mepland/chance_of_showers/media/ana_outputs/mean_pressure_value_normalized_vs_time_of_week_recent_mornings.png

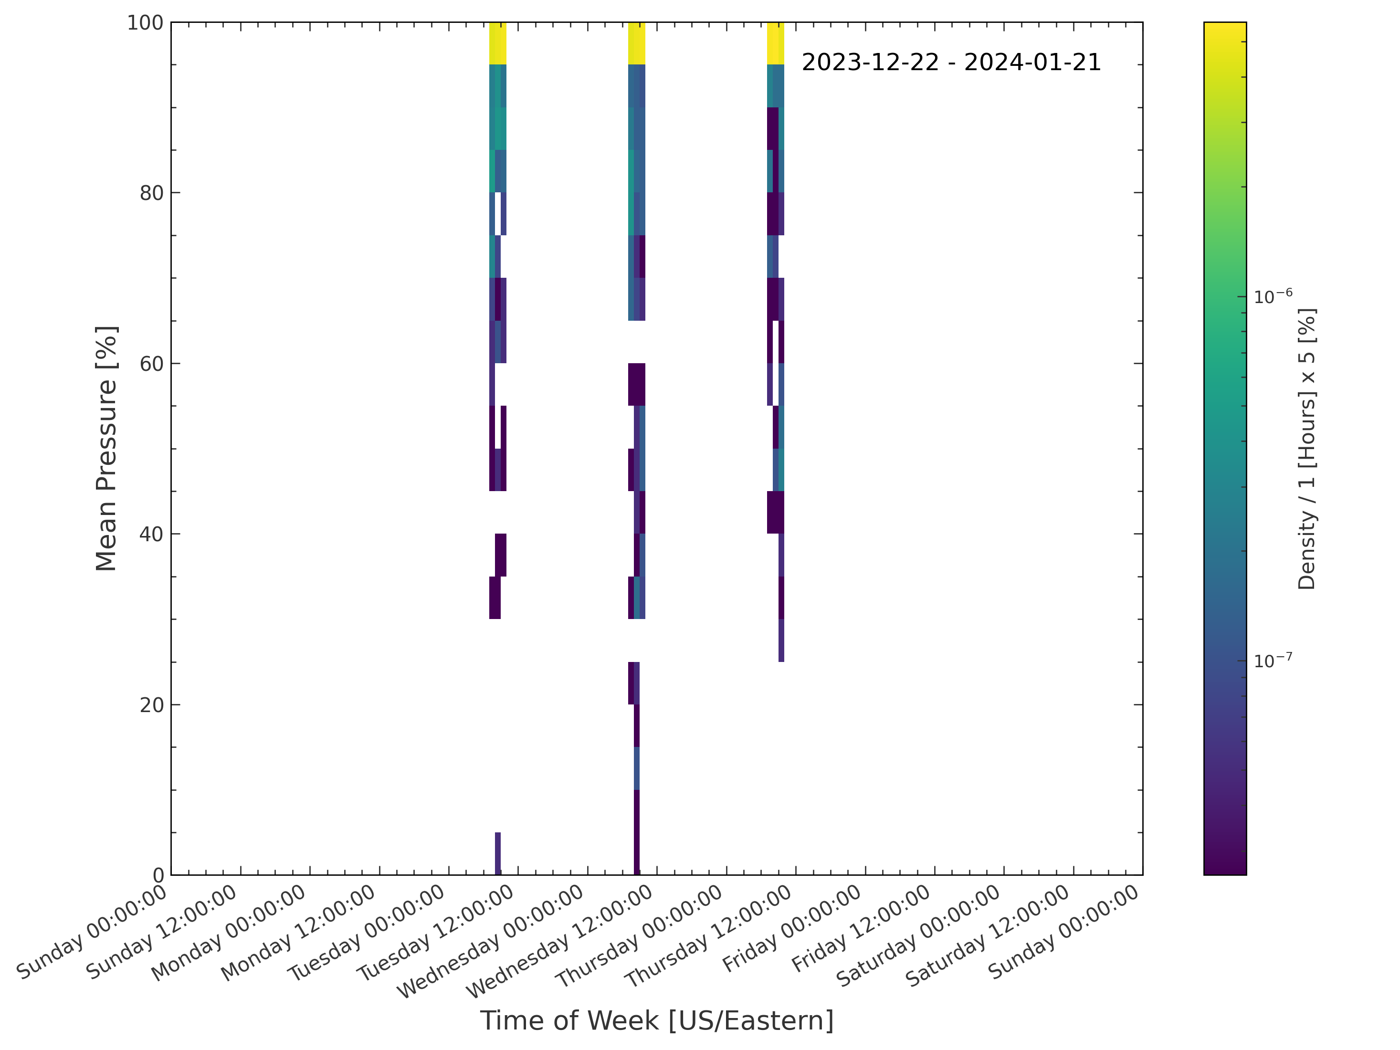
media/ana_outputs/mean_pressure_value_normalized_vs_time_of_week_recent_mornings.png
