mepland/chance_of_showers/media/screenshot_bottom.jpg

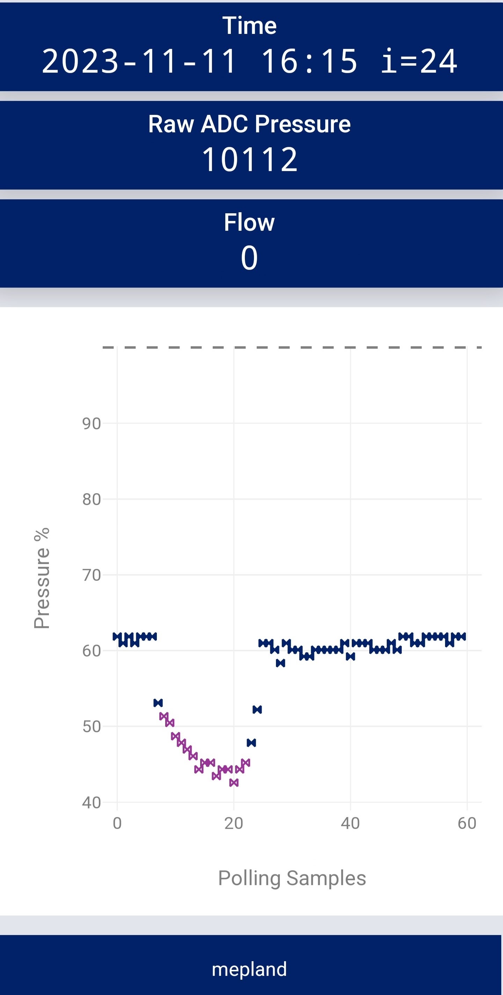
media/screenshot_bottom.jpg
