mepland/chance_of_showers/media/screenshot_top.jpg

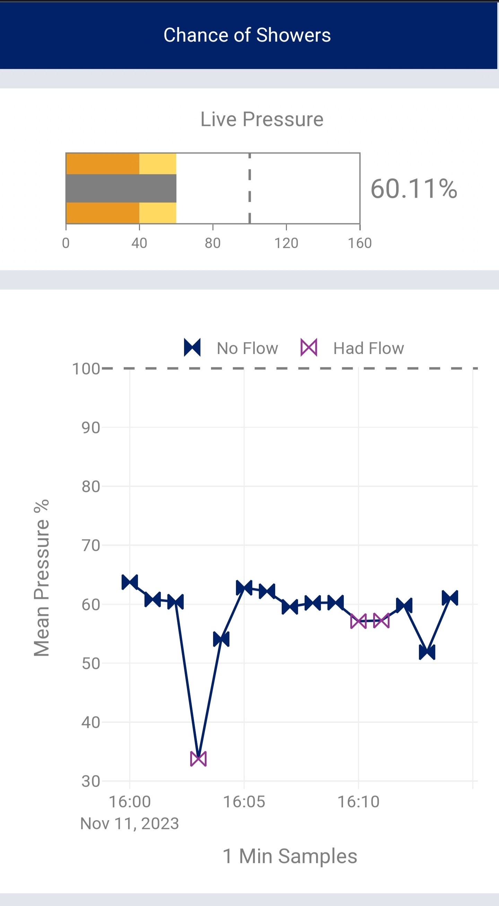
media/screenshot_top.jpg
