mepland/chance_of_showers/.vulture_ignore.py

# flake8: noqa
# pylint: skip-file
# mypy: disable-error-code="name-defined"
plot_func  # unused function (ana/plotting.py:33)
frame  # unused variable (daq/daq.py:176)
_.when_held  # unused attribute (daq/daq.py:238)
_.when_released  # unused attribute (daq/daq.py:239)
index  # unused function (daq/daq.py:343)
disconnect  # unused function (daq/daq.py:405)
_.show_server_banner  # unused attribute (daq/daq.py:426)
args  # unused variable (daq/daq.py:426)
_.when_held  # unused attribute (daq/switch_test.py:30)
_.when_released  # unused attribute (daq/switch_test.py:31)
